mlab-modules/OLED02/doc/img/IMG_20250409_185201.jpg

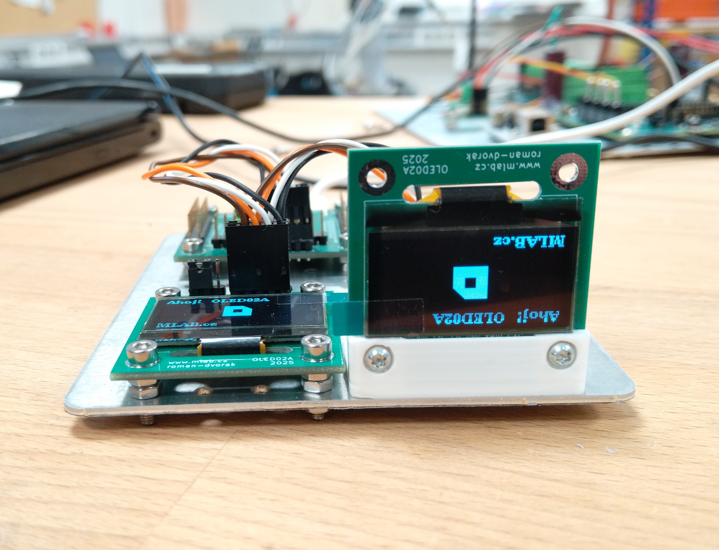
doc/img/IMG_20250409_185201.jpg
