mlab-modules/OLED02/doc/img/IMG_20250409_185218.jpg

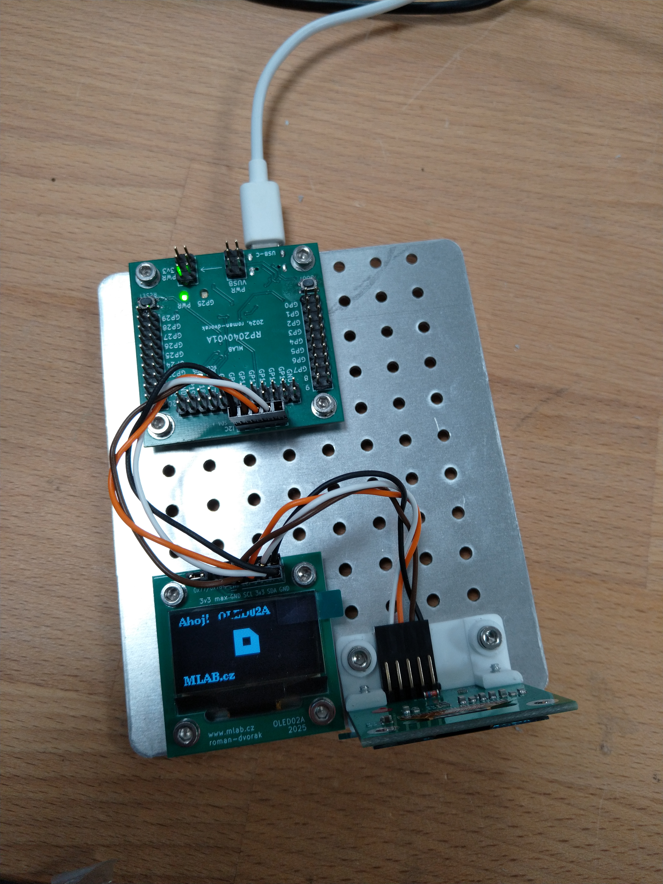
doc/img/IMG_20250409_185218.jpg
